LimeProgramming/USB-serial-mouse-adapter/images/Case-External-2.jpg

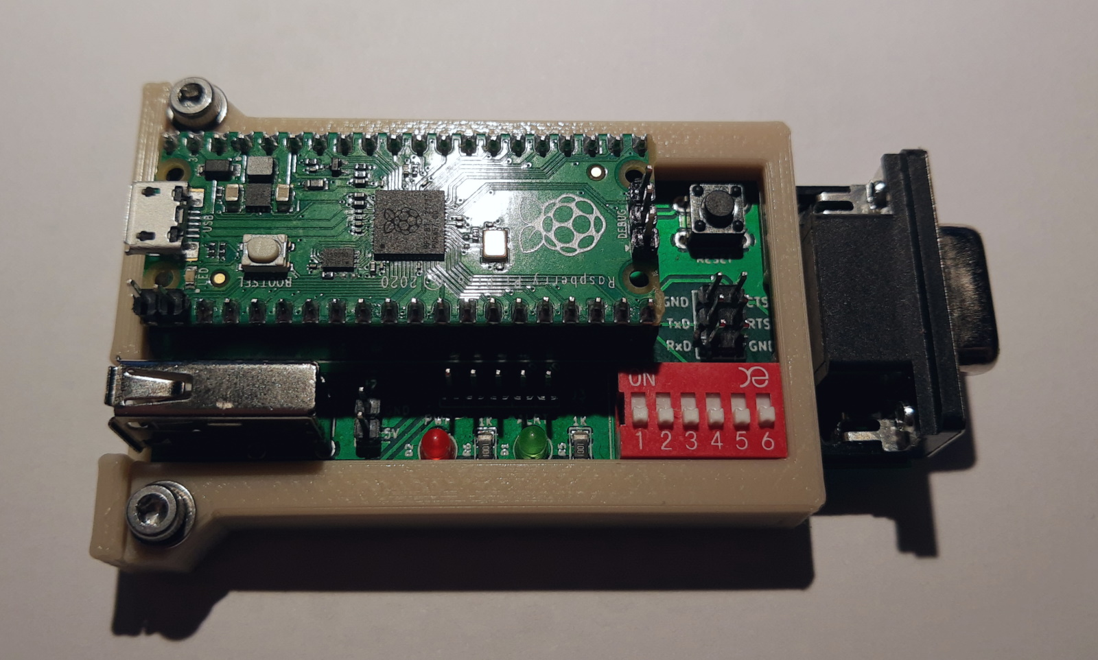
images/Case-External-2.jpg
