LimeProgramming/USB-serial-mouse-adapter/images/Case-External-3.jpg

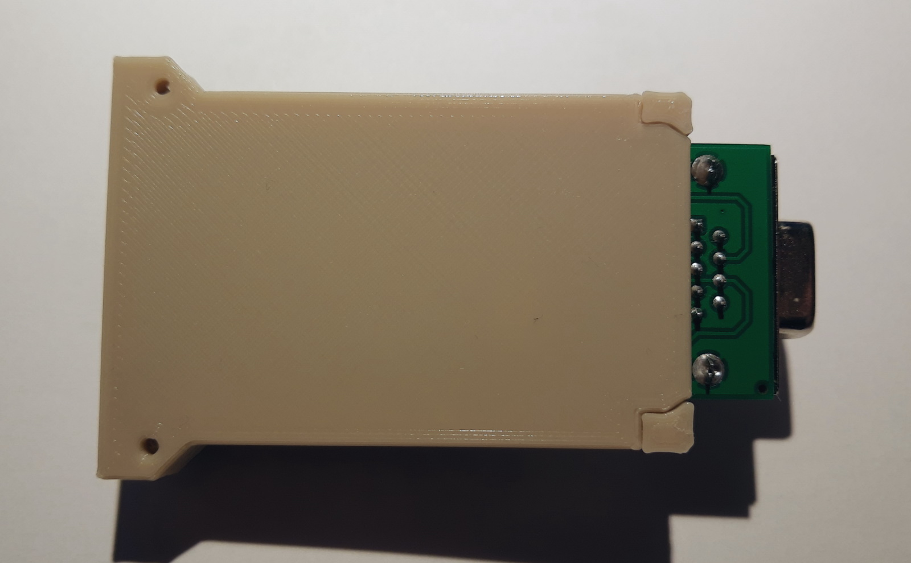
images/Case-External-3.jpg
