LimeProgramming/USB-serial-mouse-adapter/images/nopico.jpg

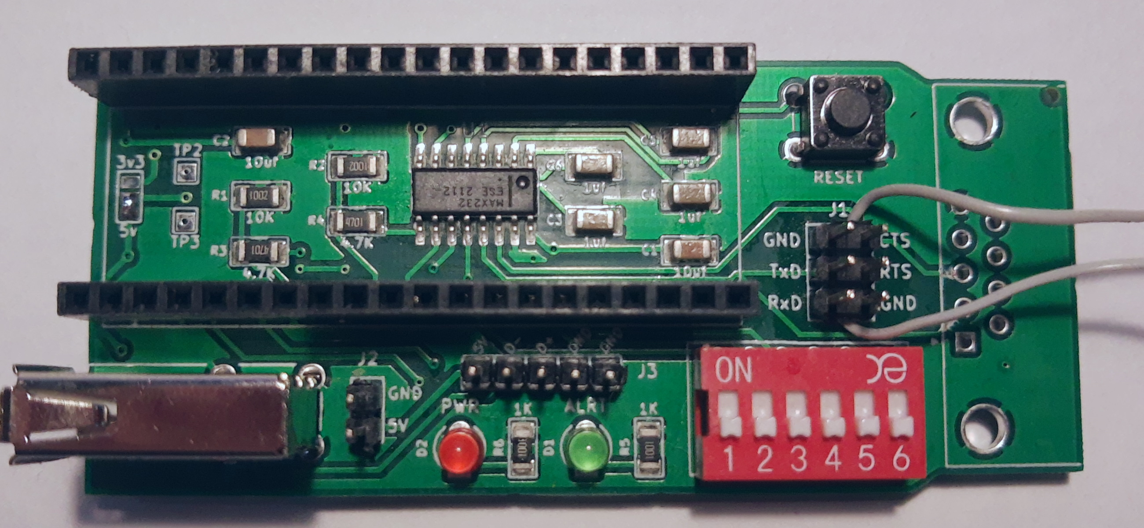
images/nopico.jpg
