LimeProgramming/USB-serial-mouse-adapter/KiCad/Phat/images/render_back.jpg

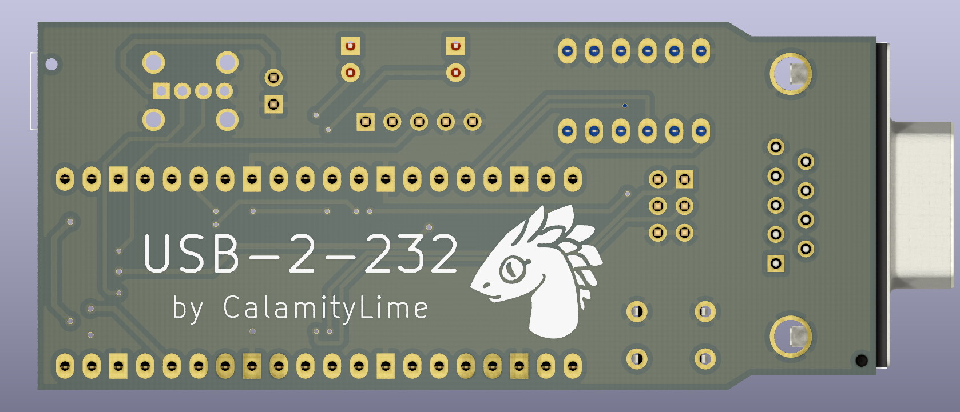
KiCad/Phat/images/render_back.jpg
