LimeProgramming/USB-serial-mouse-adapter/KiCad/Slim/images/render_front.PNG

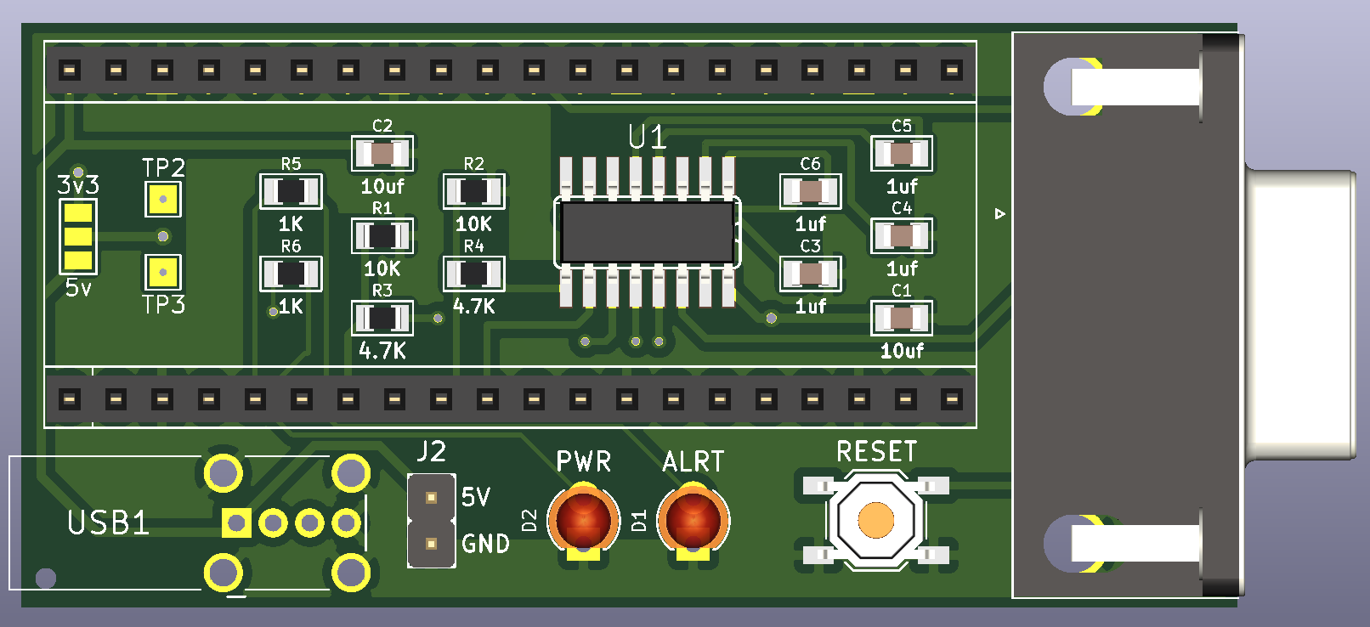
KiCad/Slim/images/render_front.PNG
