LimeProgramming/USB-serial-mouse-adapter/firmware/include/core_1.h

#include "pico.h"

#ifndef CORE_1_H_ 
#define CORE_1_H_


/*---------------------------------------*/
//              Core 1 Stuff             //
/*---------------------------------------*/

void start_core1(uint process);

void stop_core1();

#endif
